ps-nithin/zumo-jetson/docs/photo-pcb.jpg

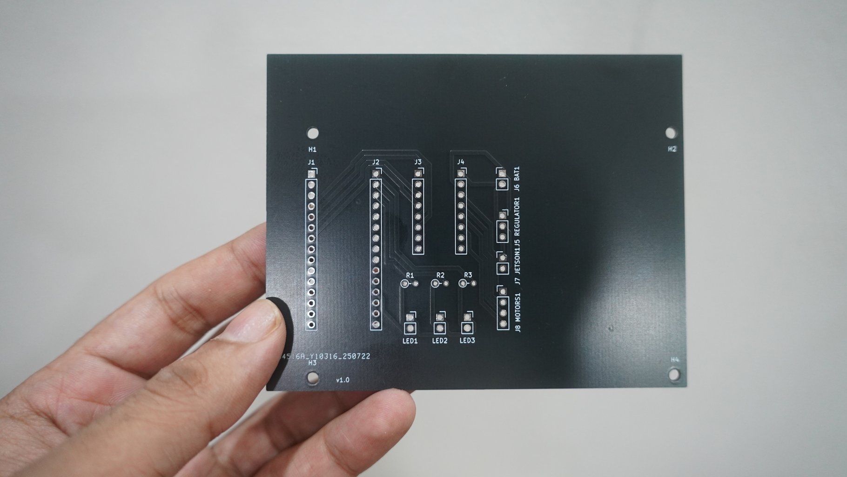
docs/photo-pcb.jpg
