ps-nithin/zumo-jetson/images/zumo-jetson1.jpg

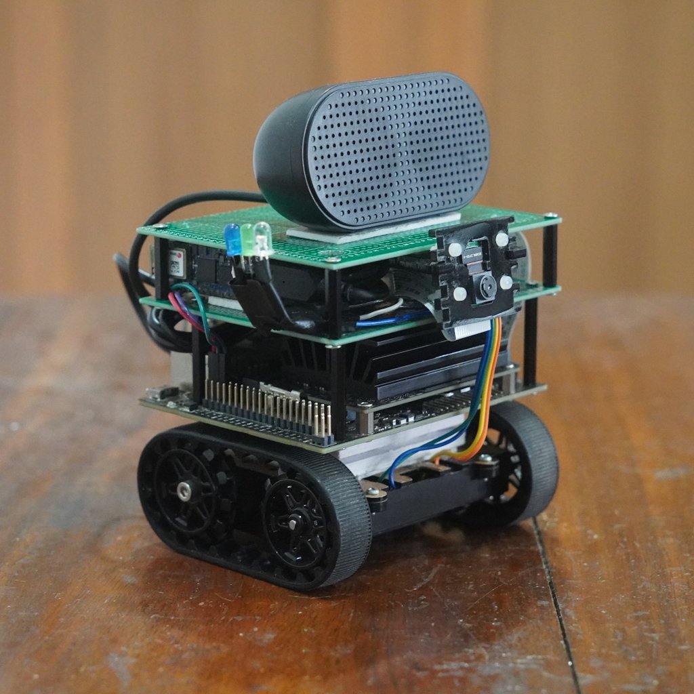
images/zumo-jetson1.jpg
