ps-nithin/zumo-jetson/scripts/images/train-hand/a.png

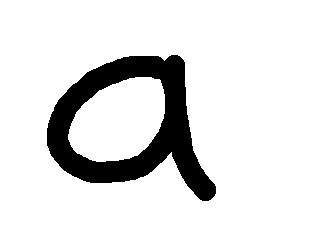
scripts/images/train-hand/a.png
