ps-nithin/zumo-jetson/scripts/images/train-hand/alpha.png

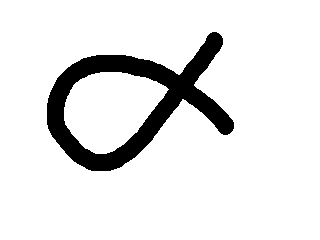
scripts/images/train-hand/alpha.png
