ps-nithin/zumo-jetson/scripts/images/train-hand/beta.png

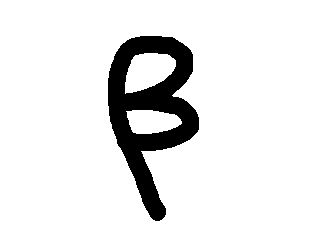
scripts/images/train-hand/beta.png
