ps-nithin/zumo-jetson/scripts/images/train-hand/c.png

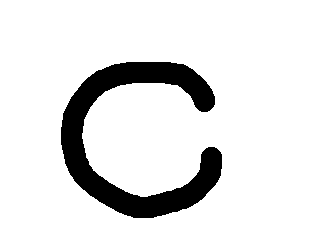
scripts/images/train-hand/c.png
