ps-nithin/zumo-jetson/scripts/images/train-hand/d.png

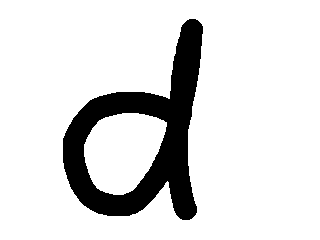
scripts/images/train-hand/d.png
