ps-nithin/zumo-jetson/scripts/images/train-hand/e.png

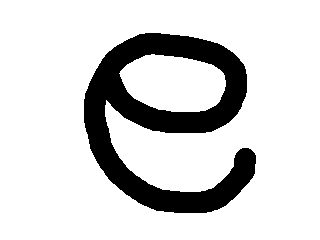
scripts/images/train-hand/e.png
