ps-nithin/zumo-jetson/scripts/images/train-hand/f.png

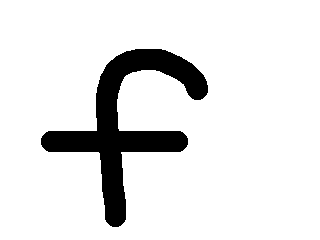
scripts/images/train-hand/f.png
