ps-nithin/zumo-jetson/scripts/images/train-hand/g.png

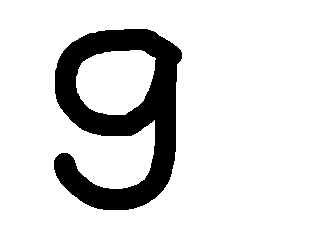
scripts/images/train-hand/g.png
