ps-nithin/zumo-jetson/scripts/images/train-hand/gamma.png

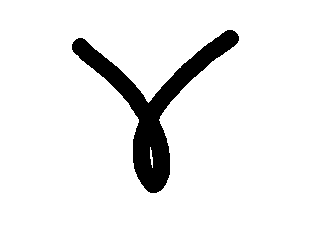
scripts/images/train-hand/gamma.png
