ps-nithin/zumo-jetson/scripts/images/train-hand/h.png

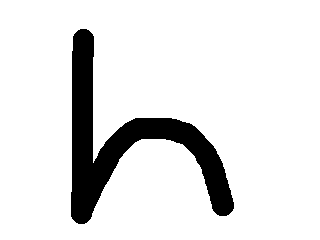
scripts/images/train-hand/h.png
