ps-nithin/zumo-jetson/scripts/images/train-hand/i.png

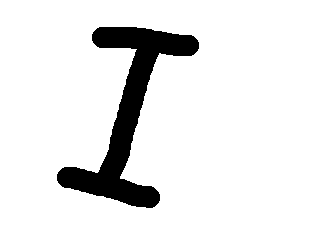
scripts/images/train-hand/i.png
