ps-nithin/zumo-jetson/scripts/images/train-hand/j.png

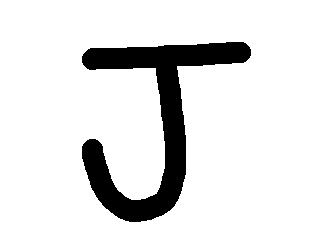
scripts/images/train-hand/j.png
