ps-nithin/zumo-jetson/scripts/images/train-hand/l.png

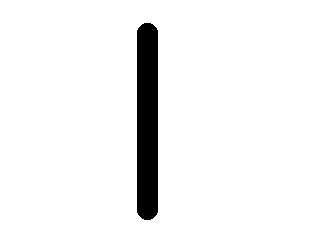
scripts/images/train-hand/l.png
