ps-nithin/zumo-jetson/scripts/images/train-hand/m.png

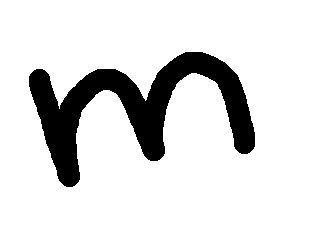
scripts/images/train-hand/m.png
