ps-nithin/zumo-jetson/scripts/images/train-hand/n.png

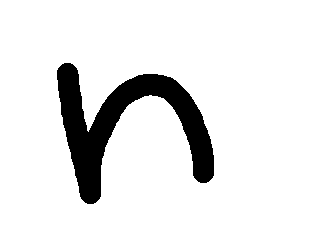
scripts/images/train-hand/n.png
