ps-nithin/zumo-jetson/scripts/images/train-hand/o.png

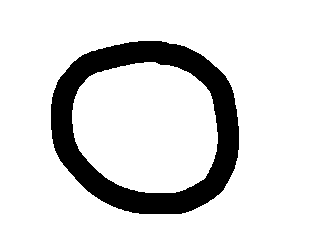
scripts/images/train-hand/o.png
