ps-nithin/zumo-jetson/scripts/images/train-hand/p.png

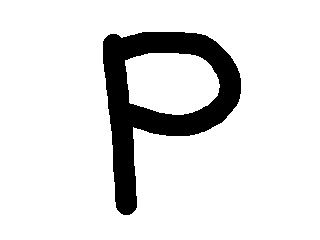
scripts/images/train-hand/p.png
