ps-nithin/zumo-jetson/scripts/images/train-hand/r.png

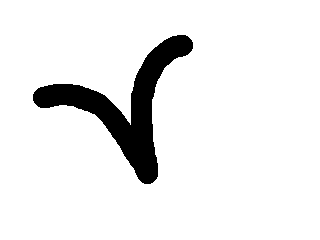
scripts/images/train-hand/r.png
