ps-nithin/zumo-jetson/scripts/images/train-hand/t.png

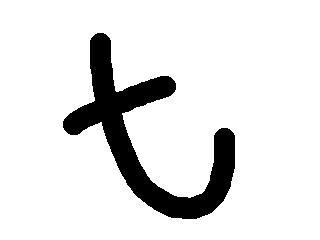
scripts/images/train-hand/t.png
