ps-nithin/zumo-jetson/scripts/images/train-hand/u.png

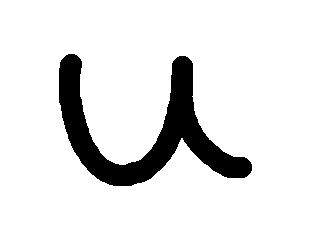
scripts/images/train-hand/u.png
