ps-nithin/zumo-jetson/scripts/images/train-hand/v.png

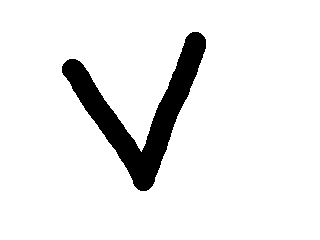
scripts/images/train-hand/v.png
