ps-nithin/zumo-jetson/scripts/images/train-hand/w.png

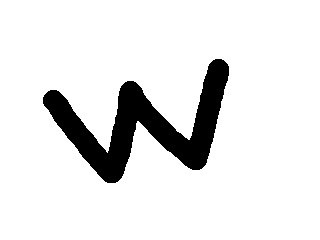
scripts/images/train-hand/w.png
