ps-nithin/zumo-jetson/scripts/images/train-hand/x.png

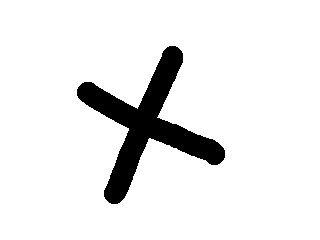
scripts/images/train-hand/x.png
