ps-nithin/zumo-jetson/scripts/images/train-hand/z.png

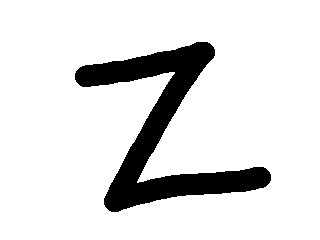
scripts/images/train-hand/z.png
