ps-nithin/zumo-jetson/scripts/pre-trained-images/backward.png

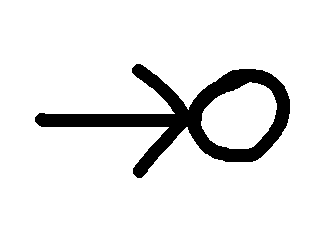
scripts/pre-trained-images/backward.png
