ps-nithin/zumo-jetson/scripts/pre-trained-images/forward.png

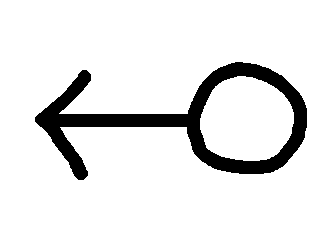
scripts/pre-trained-images/forward.png
