ps-nithin/zumo-jetson/scripts/pre-trained-images/turnleft.png

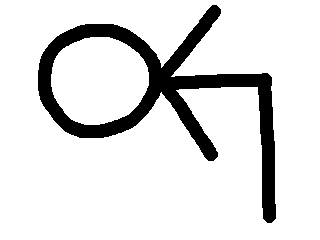
scripts/pre-trained-images/turnleft.png
