ps-nithin/zumo-jetson/scripts/pre-trained-images/turnright.png

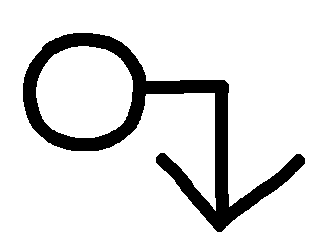
scripts/pre-trained-images/turnright.png
